timperi/c64-wedge-psu-pcb/images/c64-wedge-psu-pcb-bottom.png

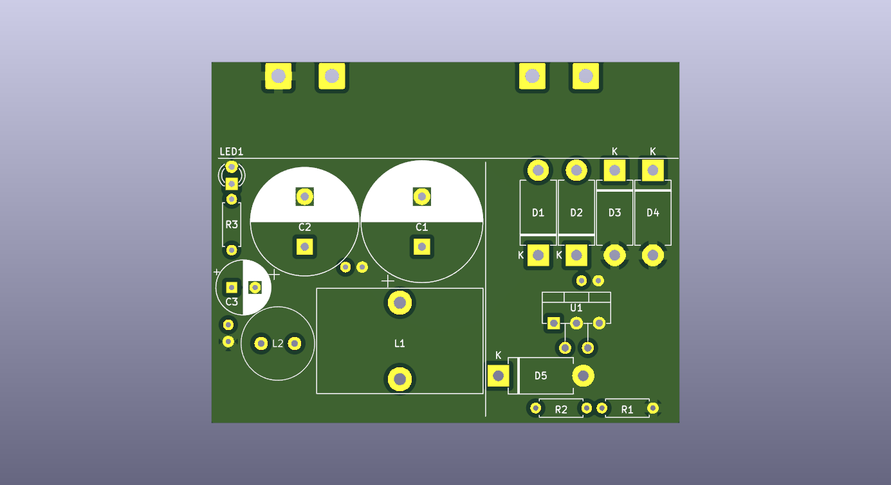
images/c64-wedge-psu-pcb-bottom.png
