timperi/c64-wedge-psu-pcb/images/c64-wedge-psu-pcb-top.png

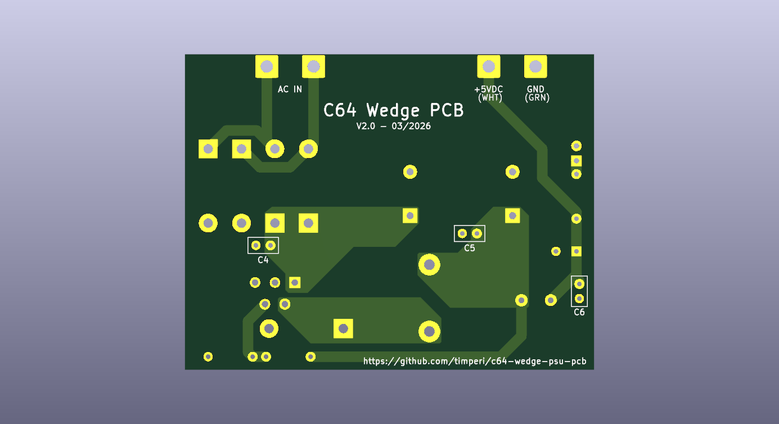
images/c64-wedge-psu-pcb-top.png
