timperi/c64-wedge-psu-pcb/images/measurements/LM2576-5mV-1us.png

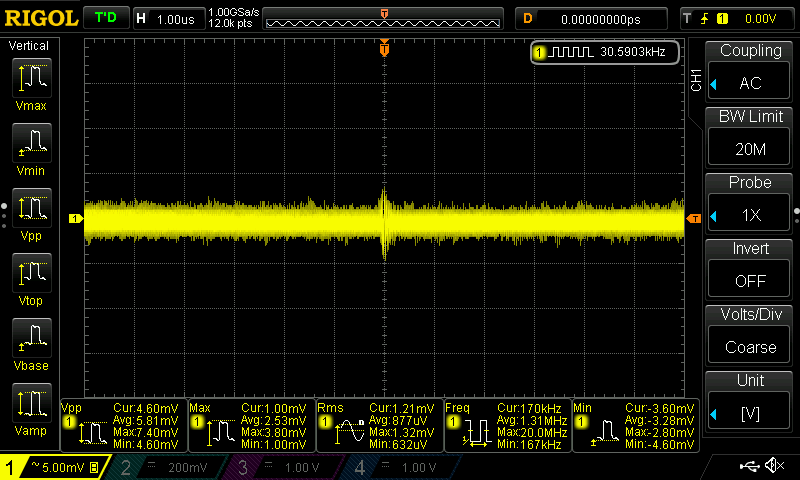
images/measurements/LM2576-5mV-1us.png
