timperi/c64-wedge-psu-pcb/images/measurements/UBEC-5mV-1us.png

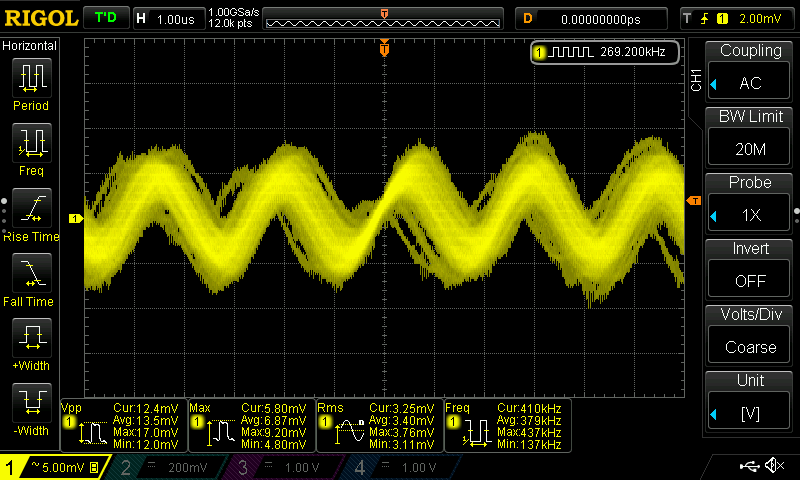
images/measurements/UBEC-5mV-1us.png
